hshahzada/automated-tourniquet/CAD STLs/AT01 - internal pneum inlet 2.stl

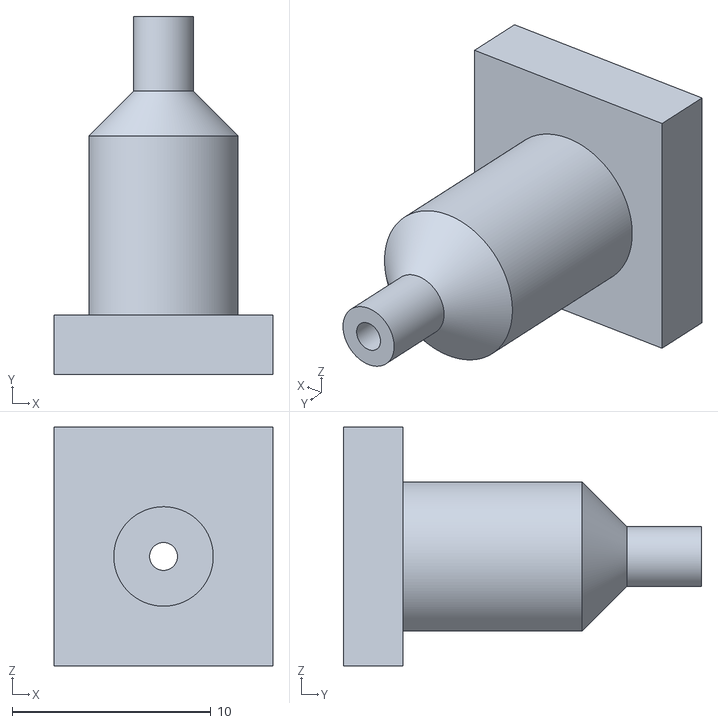
[picture p15: CAD file, 2024-05-07]
CAD STLs/AT01 - internal pneum inlet 2.stl
11.0 x 18.0 x 12.0
