hshahzada/automated-tourniquet/CAD STLs/AT01 - pcb.stl

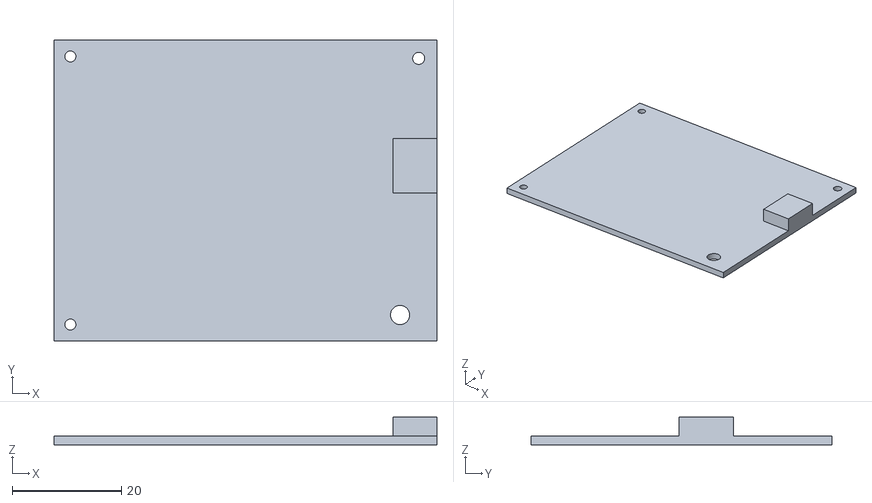
[picture p16: CAD file, 2024-05-07]
CAD STLs/AT01 - pcb.stl
70.0 x 55.0 x 5.10
