hshahzada/automated-tourniquet/CAD STLs/AT01 - cuff inlet piece.stl

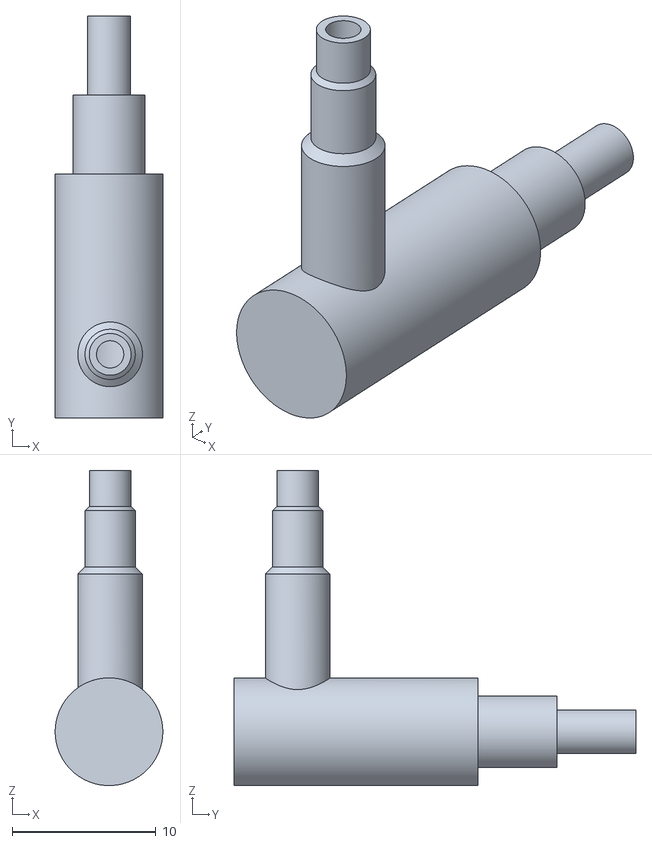
[picture p17: CAD file, 2024-05-07]
CAD STLs/AT01 - cuff inlet piece.stl
7.50 x 28.0 x 22.0
