hshahzada/automated-tourniquet/schematic_design/AT01/Sims/Draft1.asc

C1: polcap; 10µ; V=20 Irms=290m Rser=1 Lser=0 mfg="Vishay" pn="593D106M020B" type="Tantalum"
C2: cap; 100µ; V=6.3 Irms=0 Rser=0 Lser=0 mfg="Murata" pn="GRM31CR60J107KE39" type="X5R"
C3: cap; 1µ; V=4 Irms=0 Rser=0 Lser=0 mfg="Murata" pn="GRM032R60G105ME05" type="X5R"
C4: cap; 0.47µ; V=4 Irms=3.38 Rser=0.0190129 Lser=0 mfg="KEMET" pn="C0805C474K7PAC" type="X5R"
C5: cap; 10µ; V=16 Irms=0 Rser=0 Lser=0 mfg="Murata" pn="GRM21BR61C106ME15" type="X5R"
D1: schottky; 1N5817
M1: pmos; AO6407
R1: res; 100k; tol=1 pwr=0.1
R2: res; 33.2K; tol=1 pwr=0.1
U1: LT3041
V1: voltage; 5
V2: voltage; 0
Named nets: 0
.tran 0 10 0 0.1
