hshahzada/automated-tourniquet/schematic_design/AT01/Sims/Draft2.asc

R2: res; 20k
R3: res; 10k
V1: voltage; PULSE(7.4 0 0.5 9 0 0 10)
Named nets: 0, AfterDivide
.tran 0 10s 0 0.1 startup
Source = 7.4 V
Gate = 3.3 V
Drain = 0 V
Vgs(th) = -0.9 V
