hshahzada/automated-tourniquet/schematic_design/AT01/Sims/LT1935_TA01.asc

C1: cap; 4.7µ
C2: cap; 10µ
C4: cap; 10µ
D1: SCHOTTKY; 1N5817
D2: SCHOTTKY; 1N5817
L1: ind; 2.7µ; Rser=0.182
R1: RES; 70.2K
R2: RES; 10K
Rload: res; 5
U1: LT1935
V1: VOLTAGE; 5
Named nets: OUT, 0, IN
.tran 2m
LT1935 - 1.2MHz Boost DC/DC Converter in ThinSOT with 2A Switch
5V Boost Converter
Input: 2.5V to 4.8V      Output: 5V @ 1A (Vin=3.3V) or 0.6A (Vin=2.5V)
Notes:
  If the simulation model is not found please update with the "Sync Release" command from the "Tools" menu.
  It remains the customer's responsibility to verify proper and reliable operation in the actual application.
  Component substitution and printed circuit board layout may significantly affect circuit performance or reliability.
  Contact your local sales representative for assistance. This circuit is distributed to customers only for use with LTC parts.
  Copyright © 2013 Linear Technology Inc. All rights reserved.
