hshahzada/automated-tourniquet/code/at01_platformio/src/arrow_down.c

#ifdef __has_include
    #if __has_include("lvgl.h")
        #ifndef LV_LVGL_H_INCLUDE_SIMPLE
            #define LV_LVGL_H_INCLUDE_SIMPLE
        #endif
    #endif
#endif

#if defined(LV_LVGL_H_INCLUDE_SIMPLE)
    #include "lvgl.h"
#else
    #include "lvgl/lvgl.h"
#endif


#ifndef LV_ATTRIBUTE_MEM_ALIGN
#define LV_ATTRIBUTE_MEM_ALIGN
#endif

#ifndef LV_ATTRIBUTE_IMAGE_ARROW_DOWN
#define LV_ATTRIBUTE_IMAGE_ARROW_DOWN
#endif

const LV_ATTRIBUTE_MEM_ALIGN LV_ATTRIBUTE_LARGE_CONST LV_ATTRIBUTE_IMAGE_ARROW_DOWN uint8_t arrow_down_map[] = {
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
};

const lv_image_dsc_t arrow_down = {
  .header.cf = LV_COLOR_FORMAT_RGB565A8,
  .header.magic = LV_IMAGE_HEADER_MAGIC,
  .header.w = 102,
  .header.h = 82,
  .data_size = 8364 * 3,
  .data = arrow_down_map,
};
