hshahzada/automated-tourniquet/code/at01_platformio/src/img_hand.c

#ifdef __has_include
    #if __has_include("lvgl.h")
        #ifndef LV_LVGL_H_INCLUDE_SIMPLE
            #define LV_LVGL_H_INCLUDE_SIMPLE
        #endif
    #endif
#endif

#if defined(LV_LVGL_H_INCLUDE_SIMPLE)
    #include "lvgl.h"
#else
    #include "lvgl/lvgl.h"
#endif

#ifndef LV_ATTRIBUTE_MEM_ALIGN
    #define LV_ATTRIBUTE_MEM_ALIGN
#endif

#ifndef LV_ATTRIBUTE_IMAGE_IMG_HAND
    #define LV_ATTRIBUTE_IMAGE_IMG_HAND
#endif

const LV_ATTRIBUTE_MEM_ALIGN LV_ATTRIBUTE_IMAGE_IMG_HAND uint8_t img_hand_map[] = {
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
};

const lv_image_dsc_t img_hand = {
    .header.w = 100,
    .header.h = 9,
    .header.stride = 400,
    .header.cf = LV_COLOR_FORMAT_ARGB8888,
    .data = img_hand_map,
    .data_size = sizeof(img_hand_map),
};
